SarthakDas2006/ESP32-C3-IoT-Embedded-Custom_PCB/Images/PCB_editor_F.Cu_view.png

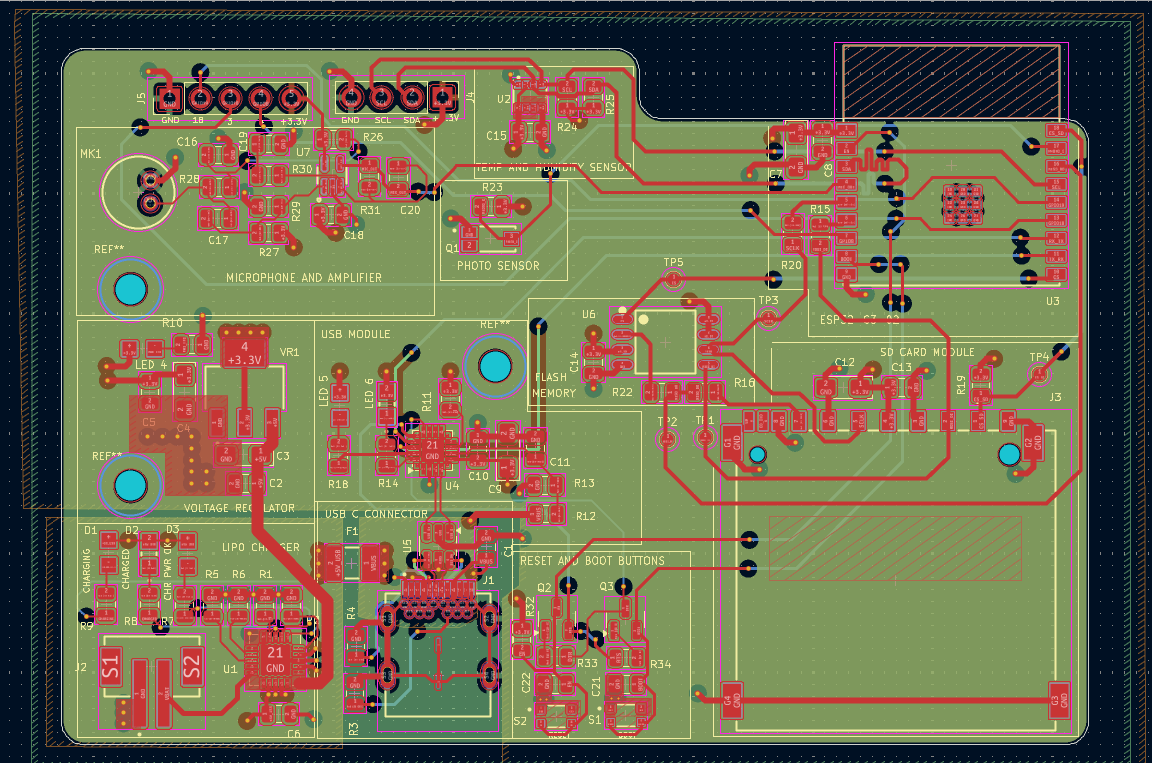
Images/PCB_editor_F.Cu_view.png
